FPSamuraiG/Senior-Design/Senior_Design.X/sleep.h

/* 
 * File:   sleep.h
 * Author: Chris
 *
 * Created on January 29, 2022, 2:42 PM
 */

#ifndef SLEEP_H
#define	SLEEP_H

#ifdef	__cplusplus
extern "C" {
#endif

#include "mcc_generated_files/mcc.h"
#include "comm_uart.h"

    extern int btn_state;
    extern int input_handled;
    
    void sleep_setup(void);
    void sleep_enter(void);
    void btn_interrupt(void);
    void tmr_interrupt(void);

#ifdef	__cplusplus
}
#endif

#endif	/* SLEEP_H */
